saper-2/pusb-adapter1/Stand/Photo1.jpg

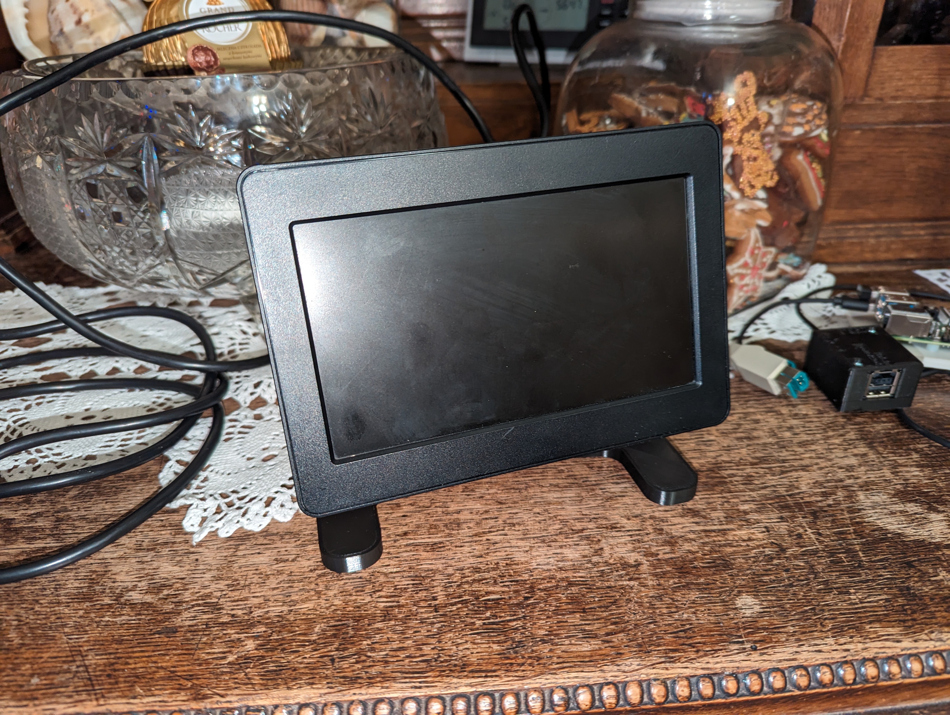
Stand/Photo1.jpg
