saper-2/pusb-adapter1/Stand/Photo2.jpg

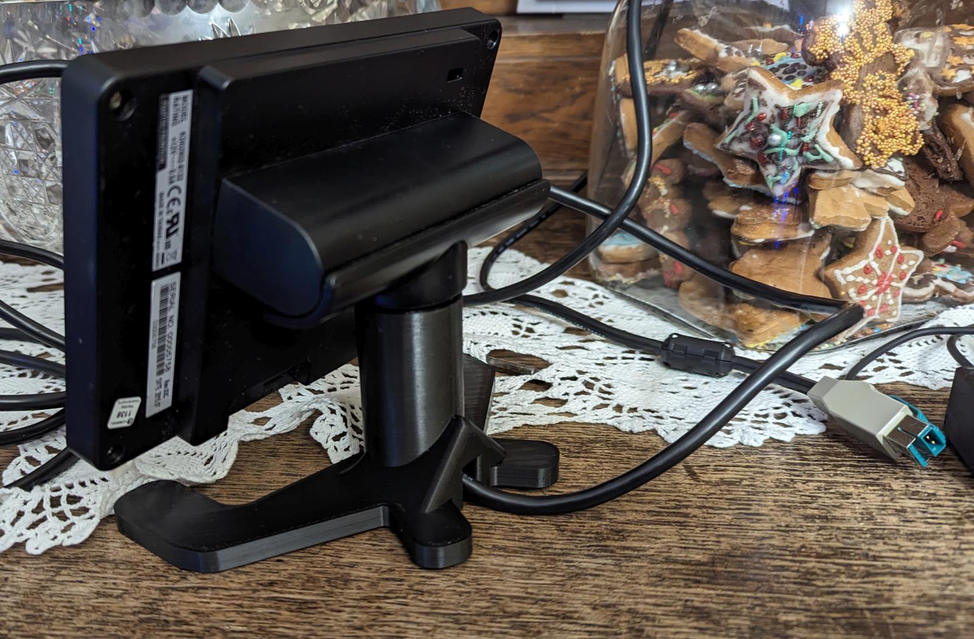
Stand/Photo2.jpg
