saper-2/pusb-adapter1/Stand/Photo3.jpg

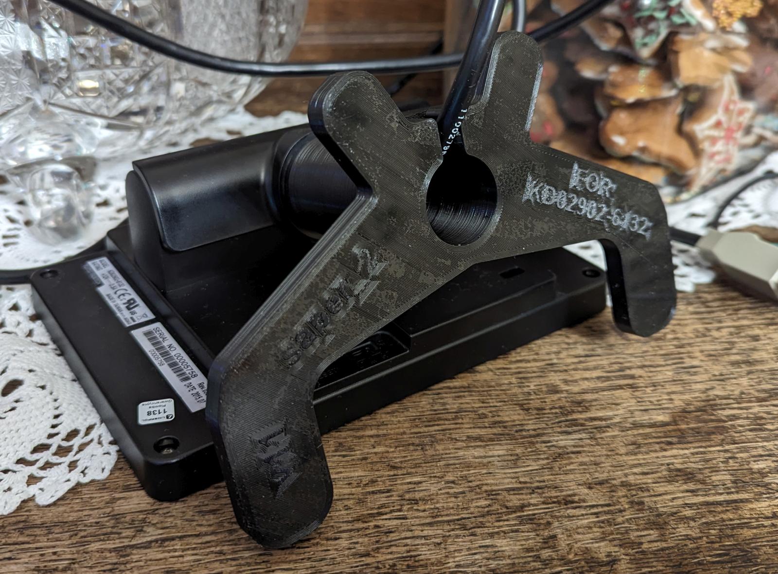
Stand/Photo3.jpg
