saper-2/pusb-adapter1/Stand/Photo4.jpg

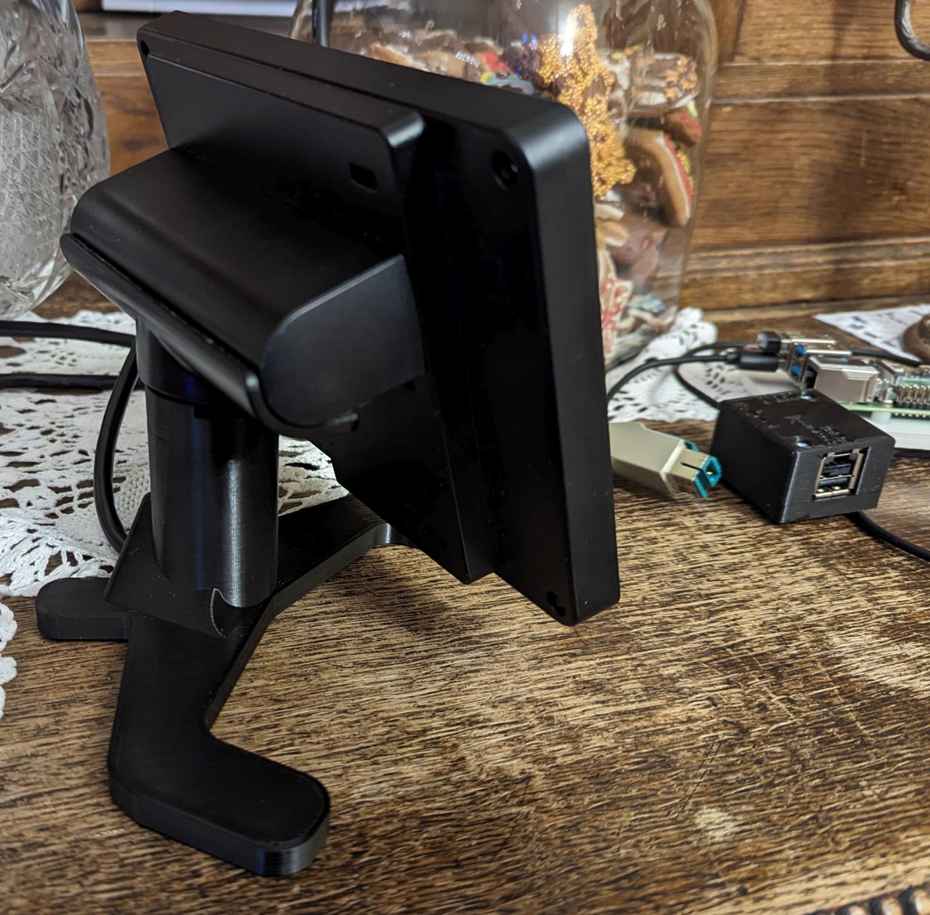
Stand/Photo4.jpg
