saper-2/pusb-adapter1/Stand/Photo5.jpg

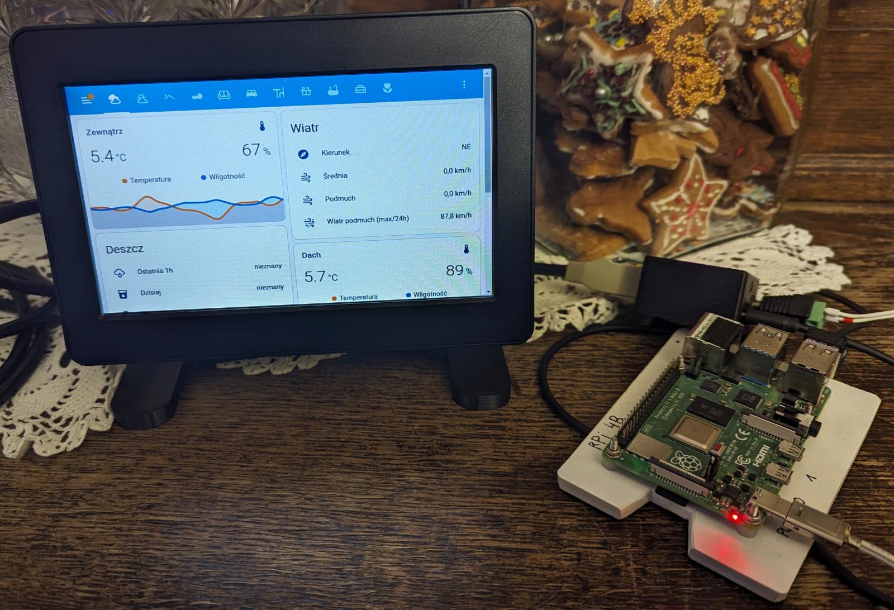
Stand/Photo5.jpg
